rulecity/EshsAurunmilla/vhdl/EshTimingProms/EshTimingPROMsTest.vhd

--------------------------------------------------------------------------------
-- Company: 
-- Engineer:
--
-- Create Date:   18:43:26 11/16/2020
-- Design Name:   
-- Module Name:   /home/ise/vhdl/EshTimingProms/EshTimingPROMsTest.vhd
-- Project Name:  EshTimingProms
-- Target Device:  
-- Tool versions:  
-- Description:   
-- 
-- VHDL Test Bench Created by ISE for module: EshTimingPROMs
-- 
-- Dependencies:
-- 
-- Revision:
-- Revision 0.01 - File Created
-- Additional Comments:
--
-- Notes: 
-- This testbench has been automatically generated using types std_logic and
-- std_logic_vector for the ports of the unit under test.  Xilinx recommends
-- that these types always be used for the top-level I/O of a design in order
-- to guarantee that the testbench will bind correctly to the post-implementation 
-- simulation model.
--------------------------------------------------------------------------------
LIBRARY ieee;
USE ieee.std_logic_1164.ALL;
 
-- Uncomment the following library declaration if using
-- arithmetic functions with Signed or Unsigned values
--USE ieee.numeric_std.ALL;
 
ENTITY EshTimingPROMsTest IS
END EshTimingPROMsTest;
 
ARCHITECTURE behavior OF EshTimingPROMsTest IS 
 
    -- Component Declaration for the Unit Under Test (UUT)
 
    COMPONENT EshTimingPROMs
    PORT(
         VA : IN  std_logic_vector(7 downto 0);
         VD : OUT  std_logic_vector(3 downto 0);
         VCS : IN  std_logic_vector(1 downto 0);
         HA : IN  std_logic_vector(7 downto 0);
         HD : OUT  std_logic_vector(3 downto 0);
         HCS : IN  std_logic_vector(1 downto 0)
        );
    END COMPONENT;
    

   --Inputs
   signal VA : std_logic_vector(7 downto 0) := (others => '0');
   signal VCS : std_logic_vector(1 downto 0) := (others => '0');
   signal HA : std_logic_vector(7 downto 0) := (others => '0');
   signal HCS : std_logic_vector(1 downto 0) := (others => '0');

 	--Outputs
   signal VD : std_logic_vector(3 downto 0);
   signal HD : std_logic_vector(3 downto 0);
 
   constant test_interval : time := 1 ns;
 
BEGIN
 
	-- Instantiate the Unit Under Test (UUT)
   uut: EshTimingPROMs PORT MAP (
          VA => VA,
          VD => VD,
          VCS => VCS,
          HA => HA,
          HD => HD,
          HCS => HCS
        );

   -- Stimulus process
   stim_proc: process
   begin		
      -- hold reset state for 100 ns.
      wait for 100 ns;	

		HCS <= "11";
		VCS <= "11";

		wait for test_interval;

		assert (HD = "ZZZZ") report "Output hasn't gone hi Z!" severity FAILURE;
		assert (VD = "ZZZZ") report "Output hasn't gone hi Z!" severity FAILURE;

		HCS <= "01";
		VCS <= "01";

		wait for test_interval;

		assert (HD = "ZZZZ") report "Output hasn't gone hi Z!" severity FAILURE;
		assert (VD = "ZZZZ") report "Output hasn't gone hi Z!" severity FAILURE;

		HCS <= "10";
		VCS <= "10";

		wait for test_interval;

		assert (HD = "ZZZZ") report "Output hasn't gone hi Z!" severity FAILURE;
		assert (VD = "ZZZZ") report "Output hasn't gone hi Z!" severity FAILURE;
		
		HCS <= "00";
		VCS <= "00";

		wait for test_interval;

		assert (HD /= "ZZZZ") report "Output shouldn't be hi Z!" severity FAILURE;
		assert (VD /= "ZZZZ") report "Output shouldn't be hi Z!" severity FAILURE;

		----------------------------------

		-- HORIZONTAL TESTS

		HA <= X"00";
		wait for test_interval;
		assert (HD = X"F") report "Unexpected value at address 00" severity FAILURE;

		HA <= X"01";
		wait for test_interval;
		assert (HD = X"F") report "Unexpected value at address 01" severity FAILURE;

		HA <= X"02";
		wait for test_interval;
		assert (HD = X"F") report "Unexpected value at address 02" severity FAILURE;

		HA <= X"03";
		wait for test_interval;
		assert (HD = X"F") report "Unexpected value at address 03" severity FAILURE;

		HA <= X"04";
		wait for test_interval;
		assert (HD = X"F") report "Unexpected value at address 04" severity FAILURE;

		HA <= X"05";
		wait for test_interval;
		assert (HD = X"F") report "Unexpected value at address 05" severity FAILURE;

		HA <= X"06";
		wait for test_interval;
		assert (HD = X"F") report "Unexpected value at address 06" severity FAILURE;

		HA <= X"07";
		wait for test_interval;
		assert (HD = X"F") report "Unexpected value at address 07" severity FAILURE;

		HA <= X"08";
		wait for test_interval;
		assert (HD = X"F") report "Unexpected value at address 08" severity FAILURE;

		HA <= X"09";
		wait for test_interval;
		assert (HD = X"F") report "Unexpected value at address 09" severity FAILURE;

		HA <= X"0A";
		wait for test_interval;
		assert (HD = X"F") report "Unexpected value at address 0A" severity FAILURE;

		HA <= X"0B";
		wait for test_interval;
		assert (HD = X"F") report "Unexpected value at address 0B" severity FAILURE;

		HA <= X"0C";
		wait for test_interval;
		assert (HD = X"F") report "Unexpected value at address 0C" severity FAILURE;

		HA <= X"0D";
		wait for test_interval;
		assert (HD = X"F") report "Unexpected value at address 0D" severity FAILURE;

		HA <= X"0E";
		wait for test_interval;
		assert (HD = X"F") report "Unexpected value at address 0E" severity FAILURE;

		HA <= X"0F";
		wait for test_interval;
		assert (HD = X"F") report "Unexpected value at address 0F" severity FAILURE;

		HA <= X"10";
		wait for test_interval;
		assert (HD = X"F") report "Unexpected value at address 10" severity FAILURE;

		HA <= X"11";
		wait for test_interval;
		assert (HD = X"F") report "Unexpected value at address 11" severity FAILURE;

		HA <= X"12";
		wait for test_interval;
		assert (HD = X"F") report "Unexpected value at address 12" severity FAILURE;

		HA <= X"13";
		wait for test_interval;
		assert (HD = X"F") report "Unexpected value at address 13" severity FAILURE;

		HA <= X"14";
		wait for test_interval;
		assert (HD = X"F") report "Unexpected value at address 14" severity FAILURE;

		HA <= X"15";
		wait for test_interval;
		assert (HD = X"F") report "Unexpected value at address 15" severity FAILURE;

		HA <= X"16";
		wait for test_interval;
		assert (HD = X"F") report "Unexpected value at address 16" severity FAILURE;

		HA <= X"17";
		wait for test_interval;
		assert (HD = X"F") report "Unexpected value at address 17" severity FAILURE;

		HA <= X"18";
		wait for test_interval;
		assert (HD = X"F") report "Unexpected value at address 18" severity FAILURE;

		HA <= X"19";
		wait for test_interval;
		assert (HD = X"F") report "Unexpected value at address 19" severity FAILURE;

		HA <= X"1A";
		wait for test_interval;
		assert (HD = X"F") report "Unexpected value at address 1A" severity FAILURE;

		HA <= X"1B";
		wait for test_interval;
		assert (HD = X"F") report "Unexpected value at address 1B" severity FAILURE;

		HA <= X"1C";
		wait for test_interval;
		assert (HD = X"F") report "Unexpected value at address 1C" severity FAILURE;

		HA <= X"1D";
		wait for test_interval;
		assert (HD = X"F") report "Unexpected value at address 1D" severity FAILURE;

		HA <= X"1E";
		wait for test_interval;
		assert (HD = X"F") report "Unexpected value at address 1E" severity FAILURE;

		HA <= X"1F";
		wait for test_interval;
		assert (HD = X"F") report "Unexpected value at address 1F" severity FAILURE;

		HA <= X"20";
		wait for test_interval;
		assert (HD = X"F") report "Unexpected value at address 20" severity FAILURE;

		HA <= X"21";
		wait for test_interval;
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

		VA <= X"F3";
		wait for test_interval;
		assert (VD = X"0") report "Unexpected value at address F3" severity FAILURE;

		VA <= X"F4";
		wait for test_interval;
		assert (VD = X"0") report "Unexpected value at address F4" severity FAILURE;

		VA <= X"F5";
		wait for test_interval;
		assert (VD = X"0") report "Unexpected value at address F5" severity FAILURE;

		VA <= X"F6";
		wait for test_interval;
		assert (VD = X"0") report "Unexpected value at address F6" severity FAILURE;

		VA <= X"F7";
		wait for test_interval;
		assert (VD = X"0") report "Unexpected value at address F7" severity FAILURE;

		VA <= X"F8";
		wait for test_interval;
		assert (VD = X"4") report "Unexpected value at address F8 (vertical)" severity FAILURE;

		VA <= X"F9";
		wait for test_interval;
		assert (VD = X"0") report "Unexpected value at address F9" severity FAILURE;

		VA <= X"FA";
		wait for test_interval;
		assert (VD = X"0") report "Unexpected value at address FA" severity FAILURE;

		VA <= X"FB";
		wait for test_interval;
		assert (VD = X"0") report "Unexpected value at address FB" severity FAILURE;

		VA <= X"FC";
		wait for test_interval;
		assert (VD = X"2") report "Unexpected value at address FC" severity FAILURE;

		VA <= X"FD";
		wait for test_interval;
		assert (VD = X"2") report "Unexpected value at address FD" severity FAILURE;

		VA <= X"FE";
		wait for test_interval;
		assert (VD = X"2") report "Unexpected value at address FE" severity FAILURE;

		VA <= X"FF";
		wait for test_interval;
		assert (VD = X"2") report "Unexpected value at address FF" severity FAILURE;


		-------------------------------

      report "Test: OK";

      wait;
   end process;

END;
